julr/usb-footswitch/CAD/KiCad/KiCad.kicad_sch

## KiCad design CAD/KiCad/KiCad.kicad_sch (2022-02-06)

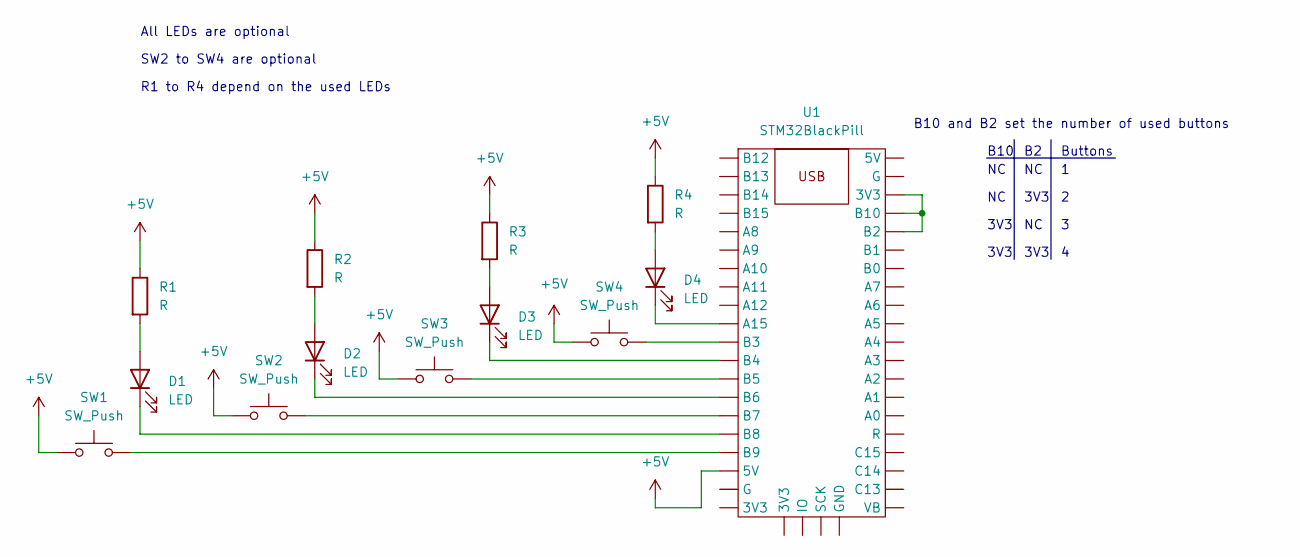
[picture p4: schematic KiCad.kicad_sch]

Parts:
D1, D2, D3, D4: LED
R1, R2, R3, R4: R
SW1, SW2, SW3, SW4: SW_Push
U1: STM32BlackPill

Connections:
+5V: R1.1, R2.1, R3.1, R4.1, SW1.1, SW2.1, SW3.1, SW4.1
unnamed: D1.1 (K), U1.
unnamed: D1.2 (A), R1.2
unnamed: D2.1 (K), U1.
unnamed: D2.2 (A), R2.2
unnamed: D3.1 (K), U1.
unnamed: D3.2 (A), R3.2
unnamed: D4.1 (K), U1.
unnamed: D4.2 (A), R4.2
unnamed: SW1.2, U1.
unnamed: SW2.2, U1.
unnamed: SW3.2, U1.
unnamed: SW4.2, U1.

Notes on the sheet:
SW2 to SW4 are optional
3V3
R1 to R4 depend on the used LEDs
Buttons
All LEDs are optional
B10
B10 and B2 set the number of used buttons
