julr/usb-footswitch/Firmware/src/tusb_config.h

/*
 * The MIT License (MIT)
 *
 * Copyright (c) 2019 Ha Thach (tinyusb.org)
 *
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
 */

#ifndef _TUSB_CONFIG_H_
#define _TUSB_CONFIG_H_

#ifdef __cplusplus
 extern "C" {
#endif

//--------------------------------------------------------------------
// COMMON CONFIGURATION
//--------------------------------------------------------------------

// defined by board.mk
#ifndef CFG_TUSB_MCU
  #error CFG_TUSB_MCU must be defined
#endif

// RHPort number used for device can be defined by board.mk, default to port 0

#define BOARD_DEVICE_RHPORT_NUM     0


// RHPort max operational speed can defined by board.mk
// Default to Highspeed for MCU with internal HighSpeed PHY (can be port specific), otherwise FullSpeed
#define BOARD_DEVICE_RHPORT_SPEED   OPT_MODE_FULL_SPEED

// Device mode with rhport and speed defined by board.mk
#define CFG_TUSB_RHPORT0_MODE     (OPT_MODE_DEVICE | BOARD_DEVICE_RHPORT_SPEED)


#define CFG_TUSB_OS OPT_OS_NONE


// CFG_TUSB_DEBUG is defined by compiler in DEBUG build
// #define CFG_TUSB_DEBUG           0

/* USB DMA on some MCUs can only access a specific SRAM region with restriction on alignment.
 * Tinyusb use follows macros to declare transferring memory so that they can be put
 * into those specific section.
 * e.g
 * - CFG_TUSB_MEM SECTION : __attribute__ (( section(".usb_ram") ))
 * - CFG_TUSB_MEM_ALIGN   : __attribute__ ((aligned(4)))
 */
#define CFG_TUSB_MEM_SECTION
#define CFG_TUSB_MEM_ALIGN          __attribute__ ((aligned(4)))

//--------------------------------------------------------------------
// DEVICE CONFIGURATION
//--------------------------------------------------------------------
#define CFG_TUD_ENDPOINT0_SIZE    64

//------------- CLASS -------------//
#define CFG_TUD_HID               2
#define CFG_TUD_CDC               0
#define CFG_TUD_MSC               0
#define CFG_TUD_MIDI              0
#define CFG_TUD_VENDOR            0

// HID buffer size Should be sufficient to hold ID (if any) + Data
#define CFG_TUD_HID_EP_BUFSIZE    8

#ifdef __cplusplus
 }
#endif

#endif /* _TUSB_CONFIG_H_ */
