julr/usb-footswitch/Firmware/src/USBDeecriptors.h

#pragma once

// Public USB Descriptor information needed by other classes
static constexpr unsigned KEYBOARD_INTERFACE {0};
static constexpr unsigned CONTROL_INTERFACE {1};
static constexpr unsigned HID_POLL_INTERVAL {10};
